richardhoman99/Single-Board-Computer/SBC Diagram.pdf

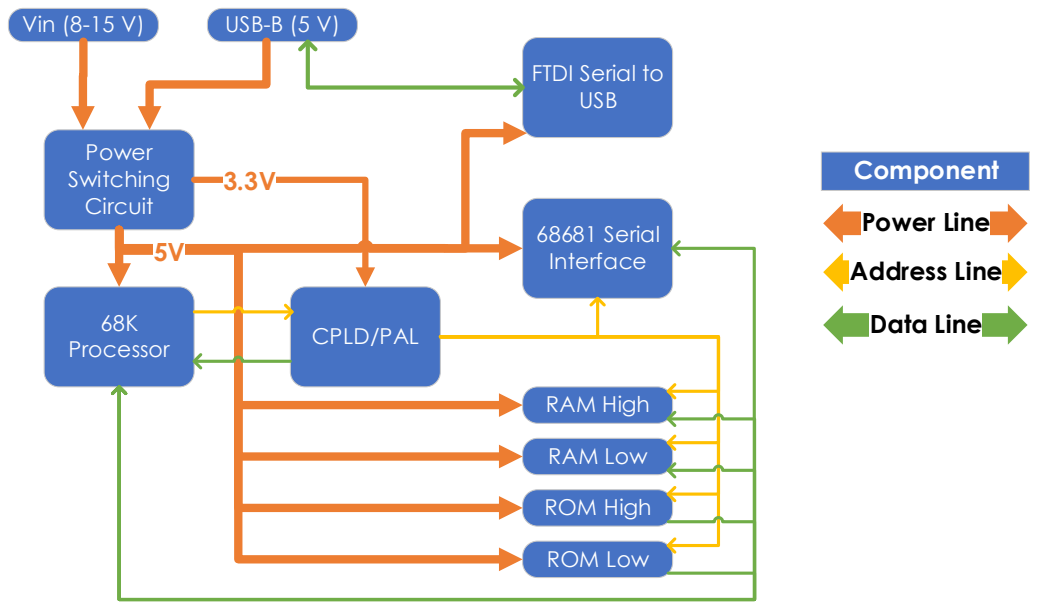
[picture p3: page 1]
USB-B (5 V); 68K Processor; ROM Low; CPLD/PAL; 68681 Serial Interface; Vin (8-15 V); Power Switching Circuit; Component; Power Line; Address Line; Data Line

FTDI Serial to
USB

RAM High

RAM Low

ROM High
