richardhoman99/Single-Board-Computer/SBC Circuit/SBC Circuit.pdf

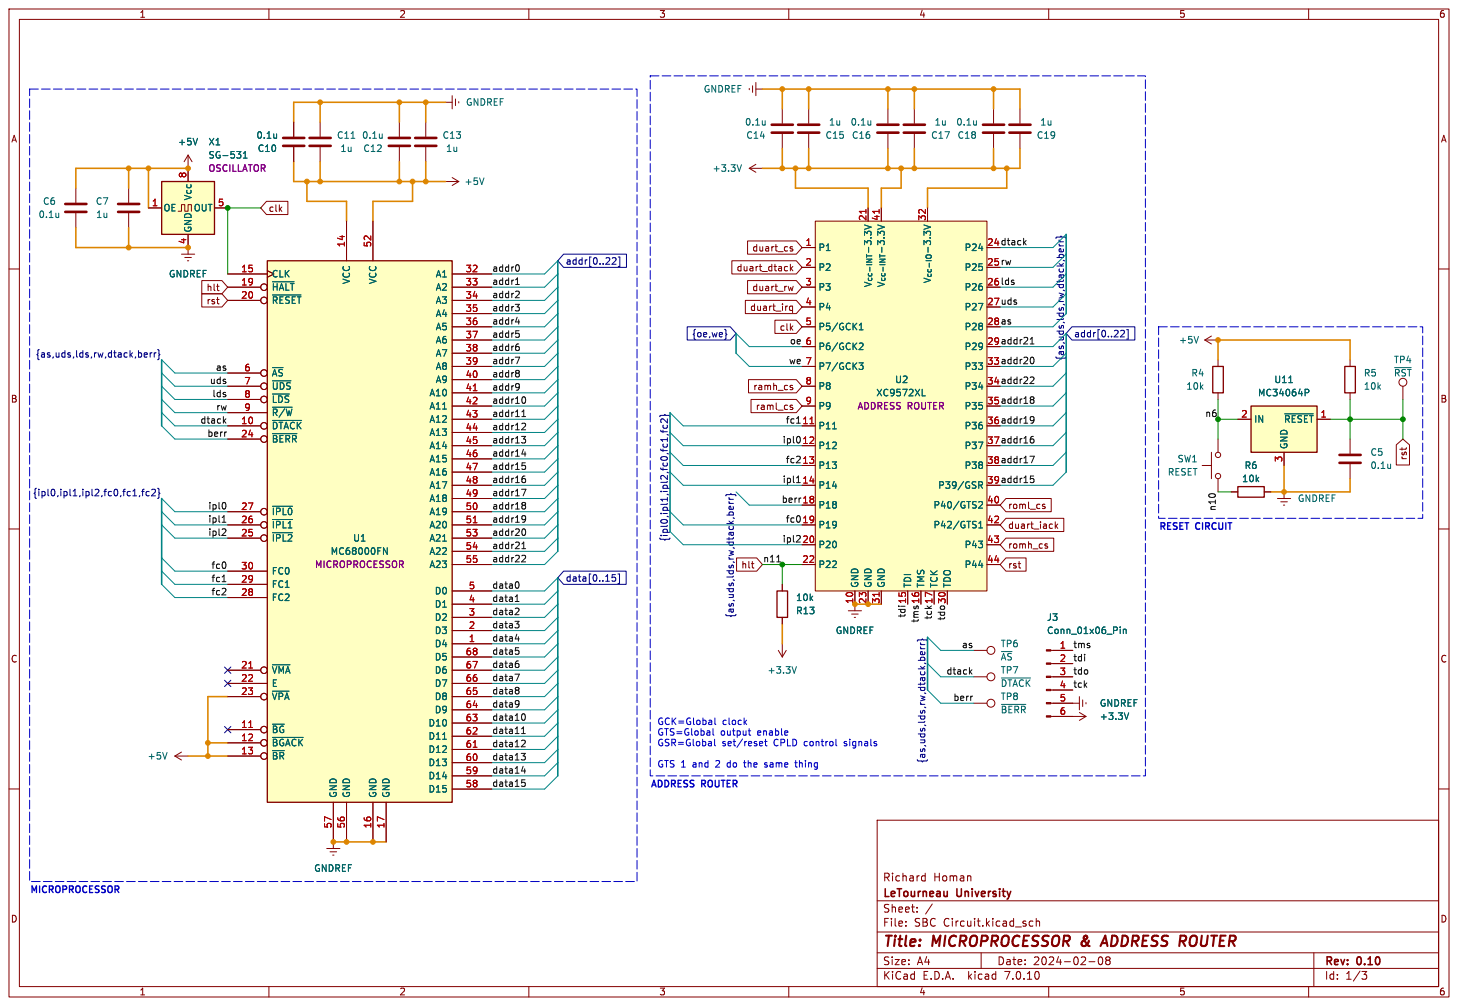
[picture p4: page 1]

Id: 1/3 Title: MICROPROCESSOR & ADDRESS ROUTER

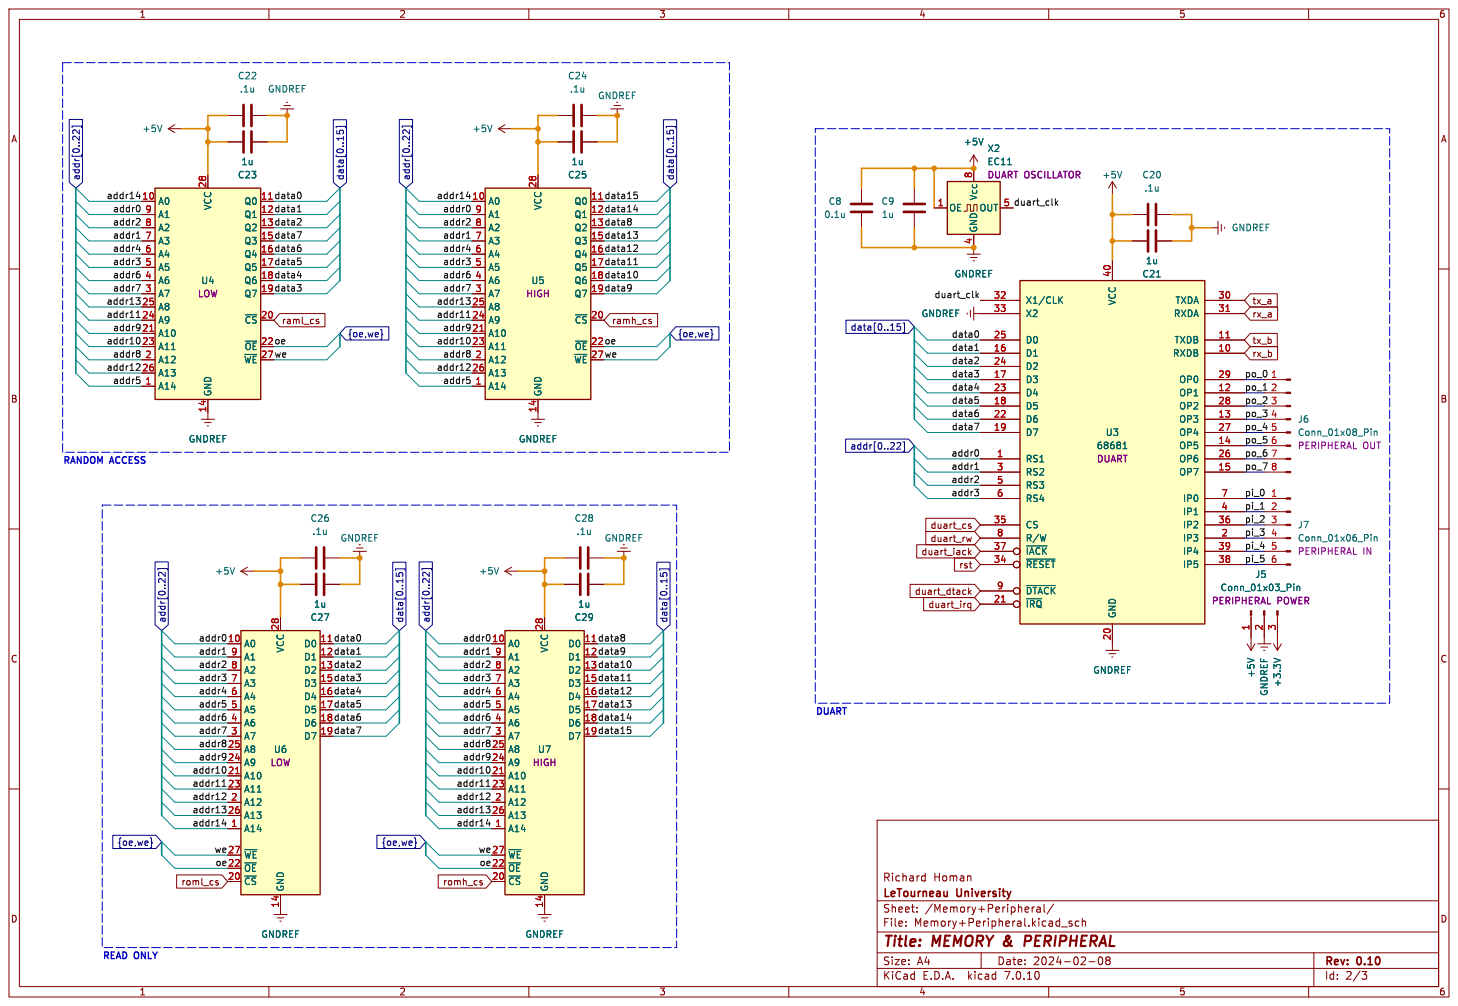
[picture p5: page 2]

Id: 2/3 Title: MEMORY & PERIPHERAL

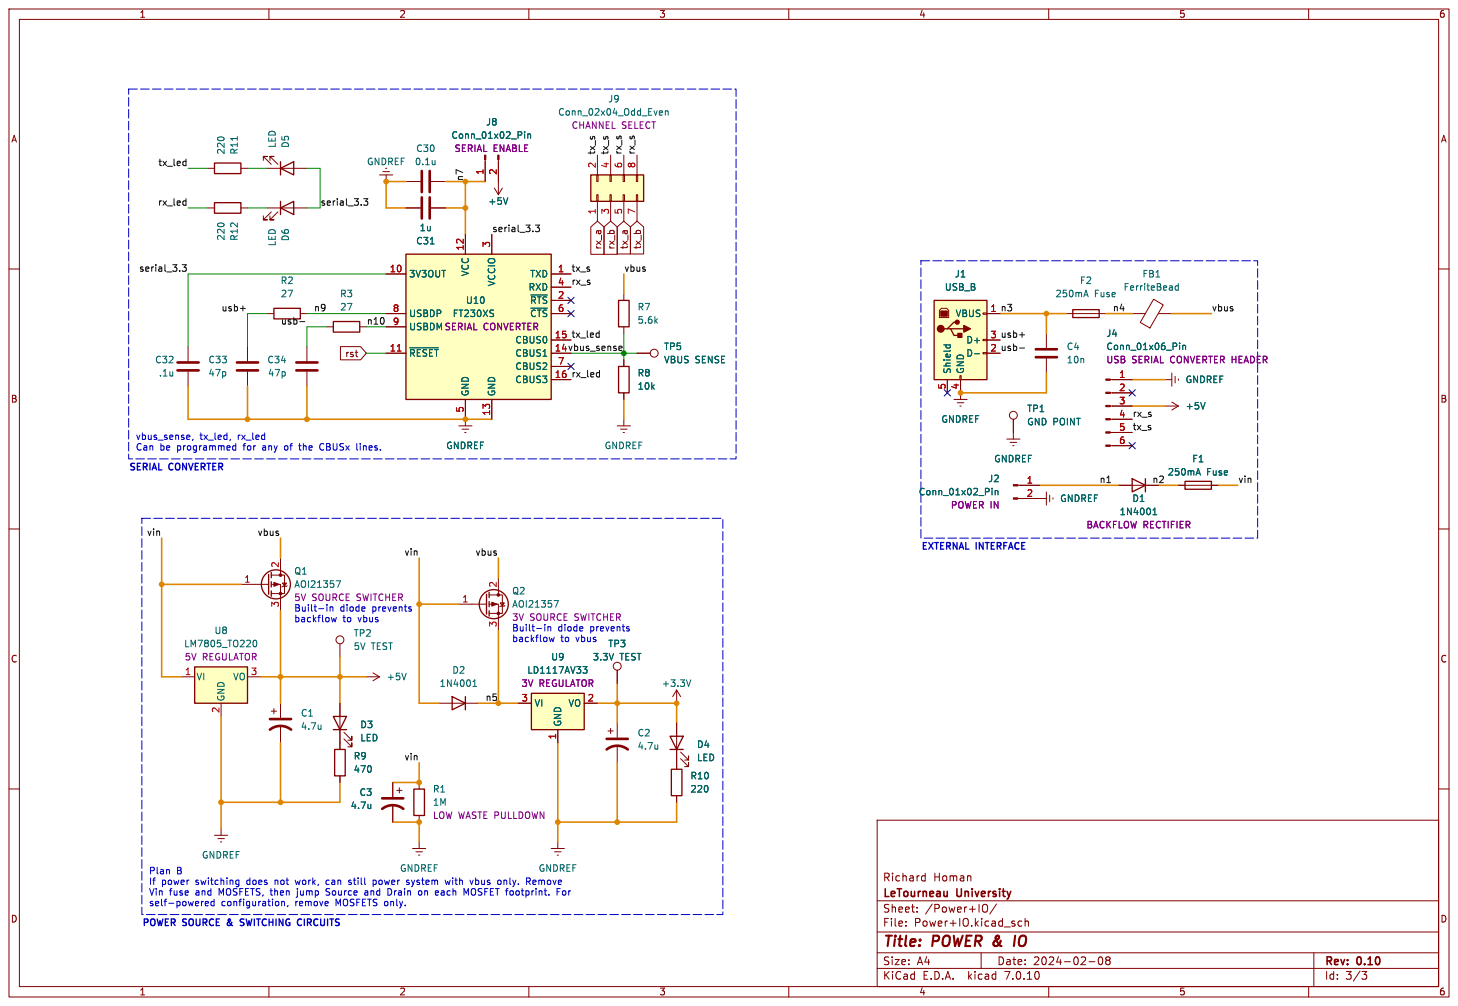
[picture p6: page 3]

J4Conn_01x06_Pin USB SERIAL CONVERTER HEADER

Id: 3/3 Title: POWER & IO
