richardhoman99/Single-Board-Computer/ems/strings.c

/*
 * strings.c
 * Richard Homan
 * 04/03/2024
 * Common strings for Enemigo Monitor System
 */

#include "strings.h"

const char welcome_str[] =
"Enemigo Monitor System\r\n\
r" REVISION " @ " __TIME__ " " __DATE__ "\r\n\
Designed by Richard Homan\r\n";
const int WELCOME_STR_LEN = ARR_LEN(welcome_str);

const char nl_str[]   = "\r\n";
const int  NL_STR_LEN = ARR_LEN(nl_str);

const char err_str[]   = "error ";
const int  ERR_STR_LEN = ARR_LEN(err_str);

#ifdef SIM
const char cur_str[]   = "_\b";
const int  CUR_STR_LEN = ARR_LEN(cur_str);

const char del_str[]   = " \b \b\b";
const int  DEL_STR_LEN = ARR_LEN(del_str);

#else

const char del_str[]   = "\b \b";
const int  DEL_STR_LEN = ARR_LEN(del_str);

#endif
