richardhoman99/Single-Board-Computer/ee/err.h

/*
 * err.h
 * Richard Homan
 * 02/17/2024
 * Command errors for Enemigo Monitor System
 */

#ifndef ERR_H
#define ERR_H

#define EMS_INV_COMM	-1
#define EMS_BAD_ARG		-2
#define EMS_NOT_HEX		-3
#define EMS_NO_EXEC		-4

#endif
